hmatuschek/dawn/firmware/clock.c

#include "clock.h"
#include "ds1307.h"
#include "pwm.h"
#include "gpio.h"

#include <avr/io.h>
#include <avr/pgmspace.h>
#include <avr/interrupt.h>
#include <avr/eeprom.h>

#include <string.h>

#include "dawnfunction.h"
#include "gpio.h"

// Specifies the maximum duration of the alarm (3h)
#define CLOCK_ALARM_MAX_SEC 10800UL

typedef enum {
  CLOCK_WAIT,
  CLOCK_ALARM,
  CLOCK_DIMUP,
  CLOCK_DIMDOWN
} ClockState;

typedef struct {
  ClockState state;
  uint16_t   value;
  uint16_t   ticks;
  uint16_t   alarmSeconds;
  DateTime   datetime;
  uint8_t    update_datetime;
} Clock;

// The singleton clock instance
volatile static Clock clock;

// Persistent storage of alarm settings
Alarm storedAlarm[CLOCK_N_ALARM] EEMEM = {
  {0,0,0}, {0,0,0}, {0,0,0}, {0,0,0}, {0,0,0}, {0,0,0}, {0,0,0} };

// Memory representation of alarm settings
static Alarm alarm_settings[CLOCK_N_ALARM];


// interpolation function for the dawn function table
uint16_t clock_map_dawn_func(uint16_t value) {
  uint8_t idx  = (value>>8);
  uint8_t frac = (value & 0x00ffu);
  uint32_t a = pgm_read_word_near(&dawn_func[idx]);
  uint32_t b = (0xff==idx) ? 0xffffu : pgm_read_word_near(&dawn_func[idx+1]);
  uint16_t x = ((0xff-frac)*a + frac*b)>>8;
  return x;
}

uint8_t update_datetime() {
  // try to get current time
  if (! ds1307_getdate((uint8_t *) &clock.datetime.year, (uint8_t *) &clock.datetime.month, (uint8_t *) &clock.datetime.day,
                       (uint8_t *) &clock.datetime.hour, (uint8_t *) &clock.datetime.minute, (uint8_t *) &clock.datetime.second)) {
    return 0;
  }
  // on success, compute day of week
  clock.datetime.dayOfWeek =
      ds1307_getdayofweek(clock.datetime.year, clock.datetime.month, clock.datetime.day);
  // done
  return 1;
}

void
clock_init() {
  // Initialize clock state
  clock.state = CLOCK_WAIT;
  clock.value = 0;
  clock.ticks = 0;
  clock.alarmSeconds = 0;

  // init keys
  key_init();

  // init pwm
  pwm_init();

  // init RTC
  ds1307_init();

  // update current time
  update_datetime();

  // Read alarm settings from EEPROM
  eeprom_read_block(alarm_settings, storedAlarm, CLOCK_N_ALARM*sizeof(Alarm));

  // Configure timer0 to trigger interrupt about every 10ms
  TCCR0A =
      // No PWM -> CTC (reset on compare match), OC0B disconnected
      (1 << WGM01);
  TCCR0B =
      // prescaler 1024
      (1 << CS02) | (1 << CS00);
  OCR0A =
      // Output compare register A  16Mhz/1024/0x9c = 100.16 Hz
      0x9c;
  TIMSK0 =
      // Interrupt on output compare A match
      (1 << OCIE0A);
}


// Tiny helper function to check if a alarm is triggered
uint8_t alarm_match() {
  for (int i=0; i<CLOCK_N_ALARM; i++) {
    // check if day of week matches
    if (0 == (alarm_settings[i].select & (1<<clock.datetime.dayOfWeek))) { continue; }
    if (alarm_settings[i].hour != clock.datetime.hour) { continue; }
    if (alarm_settings[i].minute != clock.datetime.minute) { continue; }
    if (1 < clock.datetime.second) { continue; }
    return 1;
  }
  return 0;
}


uint16_t clock_get_value() {
  return clock.value;
}

void clock_set_value(uint16_t value) {
  clock.state = CLOCK_WAIT;
  clock.value = value;
  pwm_set(clock.value);
}

void clock_get_datetime(DateTime *datetime) {
  memcpy(datetime, (DateTime *) &clock.datetime, sizeof(DateTime));
}

uint8_t clock_set_datetime(DateTime *datetime) {
  // Try to set DS1307 RTC
  if(! ds1307_setdate(datetime->year, datetime->month, datetime->day,
                      datetime->hour, datetime->minute, datetime->second)) { return 0; }
  // On success update local date-time struct
  memcpy((DateTime *) &clock.datetime, datetime, sizeof(DateTime));
  return 1;
}

uint8_t clock_set_alarm(uint8_t idx, Alarm *alarm) {
  if (idx >= CLOCK_N_ALARM) { return 0; }
  // Update memory
  memcpy(&alarm_settings[idx], alarm, sizeof(Alarm));
  // store alarm config into EEPROM
  eeprom_update_block(alarm_settings, storedAlarm, CLOCK_N_ALARM*sizeof(Alarm));
  return 1;
}

void clock_get_alarm(uint8_t idx, Alarm *alarm) {
  if (idx >= CLOCK_N_ALARM) {
    alarm->select = alarm->hour = alarm->minute = 0;
    return;
  } else {
    memcpy(alarm, &alarm_settings[idx], sizeof(Alarm));
  }
}


// Interrupt service routine for TIMER0
ISR(TIMER0_COMPA_vect) {
  cli();
  // increment tick counter
  clock.ticks++;

  // If datetime needs update -> update
  if (clock.update_datetime && update_datetime()) {
    // mark updated
    clock.update_datetime = 0;
  }

  // Every second
  if (clock.ticks == 100) {
    // reset tick counter
    clock.ticks = 0;

    // mark update date and time
    clock.update_datetime = 1;

    // If alarm -> update alarm seconds counter
    if (CLOCK_ALARM == clock.state) {
      clock.alarmSeconds++;
      if (CLOCK_ALARM_MAX_SEC <= clock.alarmSeconds) {
        clock.state = CLOCK_WAIT;
        clock.value = 0;
        pwm_set(clock.value);
      }
    }

    // Check for alarm if enabled
    if ( (CLOCK_WAIT == clock.state) && (0x00ff > clock.value) && alarm_match() && (KEY_HOLD == key(2)) ) {
      // Start alarm
      clock.state = CLOCK_ALARM;
      clock.alarmSeconds = 0;
    }
  }

  // Every 50ms -> update dawn table index
  if ((CLOCK_ALARM == clock.state) && (0 == (clock.ticks % 5))) {
    if (0xFFFF > clock.value) { clock.value++; }
    pwm_set(clock_map_dawn_func(clock.value));
  }

  if (CLOCK_DIMUP == clock.state) {
    if (0xffff == clock.value) {
      clock.state = CLOCK_WAIT;
    } else if ((0xffff-437) <= clock.value) {
      clock.value = 0xffff;
      pwm_set(clock.value);
    } else {
      clock.value += 437;
      pwm_set(clock.value);
    }
  } else if (CLOCK_DIMDOWN == clock.state) {
    if (0 == clock.value) {
      clock.state = CLOCK_WAIT;
    } else if (328 >= clock.value) {
      clock.value = 0;
      pwm_set(clock.value);
    } else {
      clock.value -= 328;
      pwm_set(clock.value);
    }
  }

  // Every 100ms -> update keys
  if (0 == (clock.ticks % 10)) {
    // Check keys:
    key_update(0);
    key_update(1);
    key_update(2);

    // Down key
    if (KEY_CLICK == key(0)) {
      clock.state = CLOCK_DIMDOWN;
    } else if (KEY_HOLD == key(0)) {
      clock.state = CLOCK_WAIT;
      if (clock.value>=(1<<10)) {
        clock.value -= (1<<10);
      } else if (clock.value) {
        clock.value = 0;
      }
      pwm_set(clock.value);
    }

    // Upkey
    else if (KEY_CLICK == key(1)) {
      clock.state = CLOCK_DIMUP;
    } else if (KEY_HOLD == key(1)) {
      clock.state = CLOCK_WAIT;
      if (clock.value<(0xffff-(1<<10))) {
        clock.value += (1<<10);
      } else if (clock.value < 0xffff) {
        clock.value = 0xffff;
      }
      pwm_set(clock.value);
    }
  }

  sei();
}
