hmatuschek/dawn/firmware/i2c.c

/*************************************************************************
* Title:    I2C master library using hardware TWI interface
* Author:   Peter Fleury <pfleury@gmx.ch>  http://jump.to/fleury
* File:     $Id: twimaster.c,v 1.3 2005/07/02 11:14:21 Peter Exp $
* Software: AVR-GCC 3.4.3 / avr-libc 1.2.3
* Target:   any AVR device with hardware TWI 
* Usage:    API compatible with I2C Software Library i2cmaster.h
**************************************************************************/
#include <inttypes.h>
#include <util/twi.h>
#include "i2c.h"
#include <avr/interrupt.h>

/* I2C clock in Hz */
#define SCL_CLOCK  100000UL

volatile static uint8_t _i2c_lock = 0;

/*************************************************************************
 Initialization of the I2C bus interface. Need to be called only once
*************************************************************************/
void i2c_init(void)
{
  /* initialize TWI clock: 100 kHz clock, TWPS = 0 => prescaler = 1 */
  
  TWSR = 0;                         /* no prescaler */
  TWBR = ((F_CPU/SCL_CLOCK)-16UL)/2;  /* must be > 10 for stable operation */

  _i2c_lock = 0;
}/* i2c_init */


uint8_t i2c_lock(void)
{
  uint8_t success;
  cli();
  if (_i2c_lock) {
    success = 0;
  } else {
    _i2c_lock = 1;
    success = 1;
  }
  sei();
  return success;
}

void i2c_unlock(void) {
  _i2c_lock = 0;
}


/*************************************************************************	
  Issues a start condition and sends address and transfer direction.
  return 0 = device accessible, 1= failed to access device
*************************************************************************/
unsigned char i2c_start(unsigned char address)
{
	// send START condition
	TWCR = (1<<TWINT) | (1<<TWSTA) | (1<<TWEN);
	// wait until transmission completed
	while(!(TWCR & (1<<TWINT)));

  // send device address
	TWDR = address;
  TWCR = (1<<TWINT) | (1<<TWEN);
	// wail until transmission completed and ACK/NACK has been received
	while(!(TWCR & (1<<TWINT)));
	// check value of TWI Status Register. Mask prescaler bits.
  return (TW_STATUS==0x18);
}/* i2c_start */


/*************************************************************************
 Terminates the data transfer and releases the I2C bus
*************************************************************************/
void i2c_stop(void)
{
    /* send stop condition */
	TWCR = (1<<TWINT) | (1<<TWEN) | (1<<TWSTO);
	
	// wait until stop condition is executed and bus released
	while(TWCR & (1<<TWSTO));

}/* i2c_stop */


/*************************************************************************
  Send one byte to I2C device
  
  Input:    byte to be transfered
  Return:   0 write successful 
            1 write failed
*************************************************************************/
unsigned char i2c_write( unsigned char data )
{	
  // send data to the previously addressed device
	TWDR = data;
  TWCR = (1<<TWINT) | (1<<TWEN);
  // wait until transmission completed
  while(! (TWCR & (1<<TWINT)));
  // Wait for ACK by slave
  //while(TW_STATUS==0x30);
	// check value of TWI Status Register. Mask prescaler bits
  return (TW_STATUS==0x28);
}/* i2c_write */


/*************************************************************************
 Read one byte from the I2C device, request more data from device 
 
 Return:  byte read from I2C device
*************************************************************************/
unsigned char i2c_readAck(void)
{
	TWCR = (1<<TWINT) | (1<<TWEN) | (1<<TWEA);
	while(!(TWCR & (1<<TWINT)));    
  return TWDR;
}/* i2c_readAck */


/*************************************************************************
 Read one byte from the I2C device, read is followed by a stop condition 
 
 Return:  byte read from I2C device
*************************************************************************/
unsigned char i2c_readNak(void)
{
	TWCR = (1<<TWINT) | (1<<TWEN);
  while (!(TWCR & (1<<TWINT)));
  return TWDR;
}/* i2c_readNak */
